dbdmks/sylvanian-fireplace/images/2leds1.6v.jpg

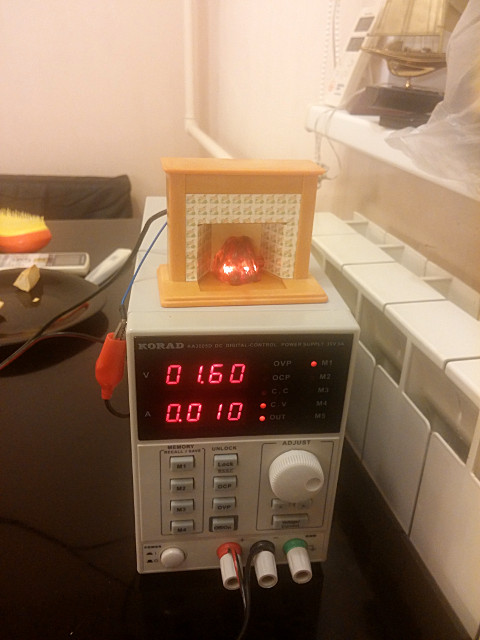
images/2leds1.6v.jpg
