dbdmks/sylvanian-fireplace/images/incandecent0.8v.jpg

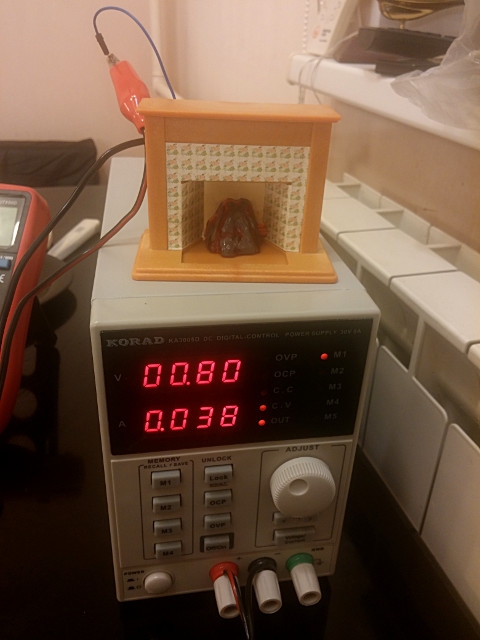
images/incandecent0.8v.jpg
