dbdmks/sylvanian-fireplace/intencities.png

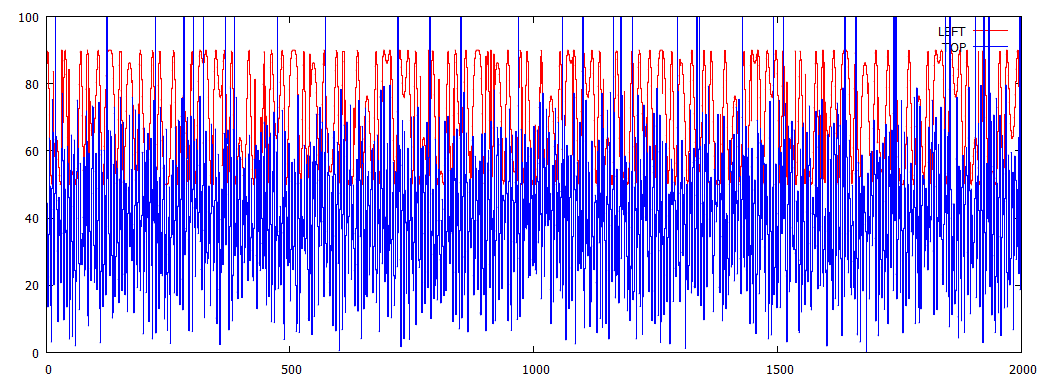
intencities.png
