dbdmks/sylvanian-fireplace/option_bytes.png

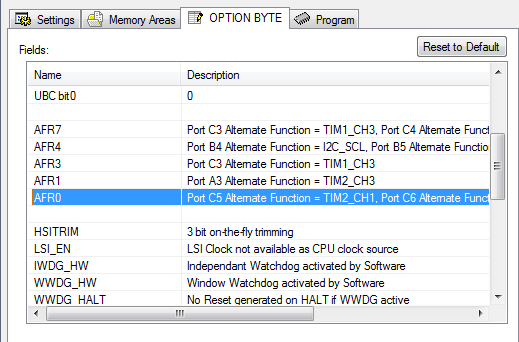
option_bytes.png
