dbdmks/sylvanian-fireplace/pwm_waves.h

#define RUNTIME 2700 // 2700 seconds = 45 min
#define FADEOUT 600 //gradually dim sides 600 seconds = 10 min before turnoff
#define FADEOUT_TOP 100 // gradually dim top 40 seconds before dimming sides
#define STEPS 30 //interrupts per second
#define WAVE_SIDE_SIZE 2000

//#define RUNTIME 2700 // 2700 seconds = 45 min
//#define FADEOUT 600 //gradually dim sides 600 seconds = 10 min before turnoff
//#define FADEOUT_TOP 100 // gradually dim top 40 seconds before dimming sides

 
const uint8_t wave_side[] = {79,86,90,89,85,79,71,63,57,53,50,50,51,53,84,58,61,62,63,64,64,63,62,60,57,55,53,51,50,50,53,90,62,68,75,82,87,90,90,87,83,77,70,64,59,54,84,50,50,50,51,52,53,54,54,54,53,52,51,50,50,50,52,55,59,65,73,80,86,89,90,86,79,70,61,54,50,51,55,62,70,78,85,89,90,89,86,51,79,75,71,68,66,65,64,64,64,65,67,70,73,77,80,84,87,89,90,88,85,79,73,66,59,54,51,50,52,56,61,67,73,78,82,85,88,89,90,90,90,90,90,90,90,90,89,87,85,82,77,71,65,58,53,50,50,54,61,69,78,85,90,89,90,78,69,61,54,51,50,52,56,61,67,72,76,80,82,84,85,86,86,86,86,84,83,80,81,73,69,64,59,54,51,50,51,54,60,66,74,68,86,89,90,89,86,81,76,71,67,63,60,57,56,54,54,54,54,55,56,58,60,64,68,73,79,84,88,90,89,86,79,71,62,55,51,50,55,62,71,79,86,90,90,87,81,75,69,63,58,55,53,51,50,50,50,50,50,50,50,50,51,52,55,58,74,67,73,79,84,88,90,89,86,81,74,67,60,55,52,50,51,53,56,60,64,67,70,73,75,76,76,76,75,74,72,69,65,61,57,54,51,50,51,55,62,86,78,85,89,90,86,78,69,61,54,50,51,54,60,67,75,81,85,88,90,90,89,89,88,87,86,62,86,87,88,89,90,90,90,88,86,81,76,70,63,57,53,50,50,53,51,65,50,78,84,87,90,90,89,87,85,82,80,78,77,76,76,77,78,79,56,84,87,89,90,90,87,83,77,69,61,55,51,50,54,61,70,79,86,90,89,85,79,71,63,57,53,50,50,51,53,56,58,61,62,63,64,64,63,62,60,57,55,53,51,50,50,53,56,62,69,76,82,87,90,90,87,83,77,70,64,59,54,52,50,50,50,81,52,53,54,54,54,53,52,51,50,50,50,70,69,59,66,73,80,86,89,90,61,79,70,61,54,50,51,55,62,70,78,85,89,90,89,86,83,79,75,71,68,66,65,64,64,64,65,67,70,73,77,80,84,87,89,90,88,85,79,73,65,59,5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
0,90,88,85,79,72,65,59,53,51};


const uint8_t wave_top[] = {54,44,37,14,25,35,64,49,23,14,3,49,75,65,43,20,38,47,100,64,53,43,30,9,45,46,37,35,39,21,51,61,77,57,36,10,28,60,48,36,36,19,14,61,56,52,46,4,16,37,54,65,33,5,22,43,59,63,24,2,21,23,54,75,61,40,26,13,26,56,34,32,26,35,32,40,58,39,23,25,55,38,72,63,11,24,8,59,39,36,25,21,25,55,73,73,47,32,21,25,54,59,44,19,25,39,49,74,54,13,3,24,60,43,54,14,15,26,60,42,47,17,30,38,100,52,66,37,35,35,23,66,64,35,29,11,12,56,54,73,17,22,29,57,55,48,33,22,15,51,37,76,68,46,19,26,43,69,51,23,19,17,50,44,49,24,12,41,48,49,71,32,42,34,54,27,76,37,33,12,38,44,72,50,56,26,19,45,56,71,46,24,19,39,38,41,59,46,6,24,67,53,56,36,18,33,60,40,65,40,9,10,45,57,64,26,42,4,48,39,75,39,48,100,6,55,51,33,41,39,13,44,52,73,24,36,29,23,46,64,46,56,10,16,35,66,31,23,7,24,29,40,49,17,3,34,53,35,53,57,38,32,18,39,67,56,17,17,30,44,69,69,55,14,36,46,64,76,22,13,31,100,63,100,29,36,37,49,58,70,63,34,7,40,39,53,70,49,45,6,49,100,63,43,37,23,46,63,43,60,37,35,42,56,76,33,48,25,19,41,50,100,56,36,10,27,60,66,63,30,27,28,42,50,43,33,14,42,68,62,56,44,24,27,40,45,66,52,10,9,45,33,59,54,19,2,31,24,40,49,37,26,37,61,65,52,40,100,32,56,64,62,66,47,7,9,37,79,58,53,16,9,23,66,57,100,29,38,32,76,57,18,16,17,46,62,47,58,29,31,16,29,45,38,55,27,35,31,58,45,46,41,45,21,59,42,65,27,34,34,52,38,30,23,21,37,58,55,61,62,29,13,21,60,36,57,27,26,24,65,40,40,32,25,33,58,68,29,47,25,48,14,68,66,36,37,17,23,64,65,38,9,22,20,54,48,72,9,38,19,33,60,54,100,35,19,25,36,40,43,20,32,38,72,46,36,9,4,21,66,60,43,48,28,40,2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
